vossi1/v8502/hdl/V8502.v

/*
   V8502 - Adapter to use 6502 in 8502-based system (C128)
   Original Design: Copyright (c) 2024 Vossi
	www.mos6502.net
	
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
   V8502.v: Implements 7bit I/O Port and Address Enable Control
	
	v.1 version:
	- initial (base is V6510 v.3)
*/

module V8502(	input [15:0]address_6502,
				output [15:0]address_8502,
				inout [7:0]data_6502,
				inout [7:0]data_8502,
				inout [6:0]ioport,
				input r_w_6502,
				output r_w_8502,
				input phi1,
				input phi2,
				input aec,
//				input rdy,				// not used
				input _reset
            	);

reg [7:0]data_out;				// databus to port
reg [7:0]data_6502_out;			// databus to CPU
reg [6:0]port_in_latched;		// port input latches
wire [6:0]port_out;
wire [7:0]port_data;
reg [7:0]port_ddr_reg;			// register $0000
reg [7:0]port_data_reg;			// register $0001
wire io_select;
reg io_select_latched;
reg write1;						// latched W/_R
wire oe_data_in, oe_io_data, oe_d;
wire rd_0x00, rd_0x01, wr_0x00, wr_0x01;
wire phi2_th;
wire delay1, delay2, delay3, delay4;//, delay5, delay6;	// TH delay wires

assign address_8502 = 	(aec ? address_6502 : 16'bz);	// address only with AEC = high
assign r_w_8502 = 		(aec ? r_w_6502 : 1'bz);		// R/_W only with AEC = high
assign data_6502 = 		data_6502_out;					// data read output to 6502
assign data_8502 = 		data_out;						// data write output to board
assign ioport = 		port_out;						// output to io-port

always @(negedge phi1)			// latch signals at phi1 falling edge
begin
	write1 <= !r_w_6502;				// latched W/_R
	io_select_latched <= io_select;		// latch io_select
	port_in_latched <= ioport;			// sample port inputs
end

// phi2 delay for databus hold time ( about 30ns - each inverter needs 5ns )
(*S = "TRUE"*) inverter inv1(phi2, delay1);		//(prefix *S prevents removing in optimization)
(*S = "TRUE"*) inverter inv2(delay1, delay2);
(*S = "TRUE"*) inverter inv3(delay2, delay3);
(*S = "TRUE"*) inverter inv4(delay3, delay4);
(*S = "TRUE"*) inverter inv5(delay4, delay5);
(*S = "TRUE"*) inverter inv6(delay5, delay6);
assign phi2_th = phi2 | delay6;		// phi high 30ns extended (typical TH time mos 8502 datasheet)

assign oe_data_in = !io_select_latched & phi2_th; 					// data in enable
assign oe_io_data = io_select_latched & phi2_th; 					// io in enable
assign oe_d 		= write1 & !io_select_latched &aec & phi2_th;	// data out enable
assign io_select 	= address_6502[15:1] == 0;						// port $0000 or $0001 selected
assign rd_0x00 	= !write1 & io_select & phi2_th & !address_6502[0];	// read ddr register 0x00
assign rd_0x01 	= !write1 & io_select & phi2_th & address_6502[0];	// read data register 0x01
assign wr_0x00 	= write1 & io_select & !address_6502[0];			// write ddr register 0x00
assign wr_0x01 	= write1 & io_select & address_6502[0];				// write data register 0x01

always @(negedge phi2, negedge _reset)
begin
	if(!_reset) begin 					// reset all register
		port_ddr_reg <= 0;
		port_data_reg <= 0;
		end
	else if(wr_0x00)					// write ddr register
		port_ddr_reg <= data_6502;
	else if(wr_0x01)					// write data register
		port_data_reg <= data_6502;
end

assign port_data[0] = (port_ddr_reg[0] ? port_data_reg[0] : port_in_latched[0]);	// port read
assign port_data[1] = (port_ddr_reg[1] ? port_data_reg[1] : port_in_latched[1]);
assign port_data[2] = (port_ddr_reg[2] ? port_data_reg[2] : port_in_latched[2]);
assign port_data[3] = (port_ddr_reg[3] ? port_data_reg[3] : port_in_latched[3]);
assign port_data[4] = (port_ddr_reg[4] ? port_data_reg[4] : port_in_latched[4]);
assign port_data[5] = (port_ddr_reg[5] ? port_data_reg[5] : port_in_latched[5]);
assign port_data[6] = (port_ddr_reg[6] ? port_data_reg[6] : port_in_latched[6]);
assign port_data[7] = (port_ddr_reg[7] ? port_data_reg[7] : 0);		// no io pin

assign port_out[0] = (port_ddr_reg[0] ? port_data_reg[0] : 1'bz);			// port outputs
assign port_out[1] = (port_ddr_reg[1] ? port_data_reg[1] : 1'bz);
assign port_out[2] = (port_ddr_reg[2] ? port_data_reg[2] : 1'bz);
assign port_out[3] = (port_ddr_reg[3] ? port_data_reg[3] : 1'bz);
assign port_out[4] = (port_ddr_reg[4] ? port_data_reg[4] : 1'bz);
assign port_out[5] = (port_ddr_reg[5] ? port_data_reg[5] : 1'bz);
assign port_out[6] = (port_ddr_reg[6] ? port_data_reg[6] : 1'bz);

always @(*)		// databus read/write
begin
	if(oe_d) begin	
		data_6502_out = 8'bz;			// outputs to CPU hiz
		data_out = data_6502;					// data out to board (only if not IO-register write)
		end
	else begin
		data_out = 8'bz;				// outputs to board hiz
		if(rd_0x00 & oe_io_data)				// read io-port ddr reg
			data_6502_out = port_ddr_reg;
		else if(rd_0x01 & oe_io_data)			// read io-port data reg
			data_6502_out = port_data;
		else if(oe_data_in)						// read data
			data_6502_out = data_8502;
		else 
		data_6502_out = 8'bz;			// outputs to CPU hiz
		end
	end
endmodule
